VinFar/Tiki-Desklamp/Photos/IMG_20170602_134848.jpg

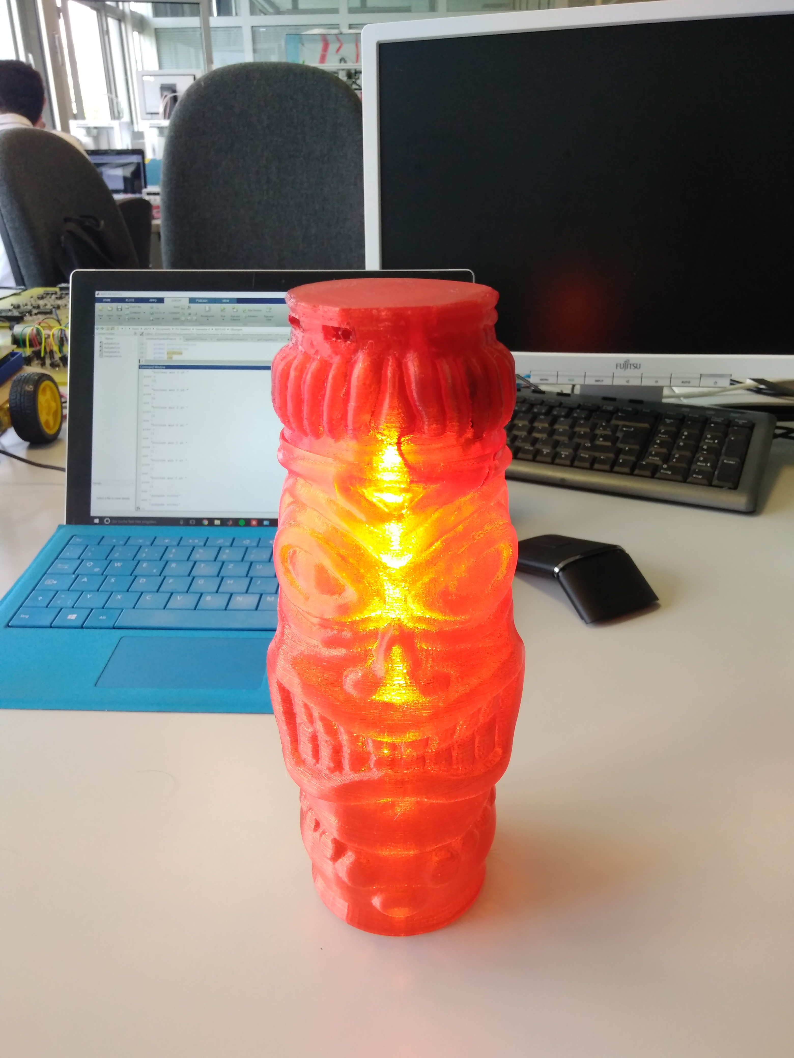
Photos/IMG_20170602_134848.jpg
