VinFar/Tiki-Desklamp/Photos/IMG_20170602_134851.jpg

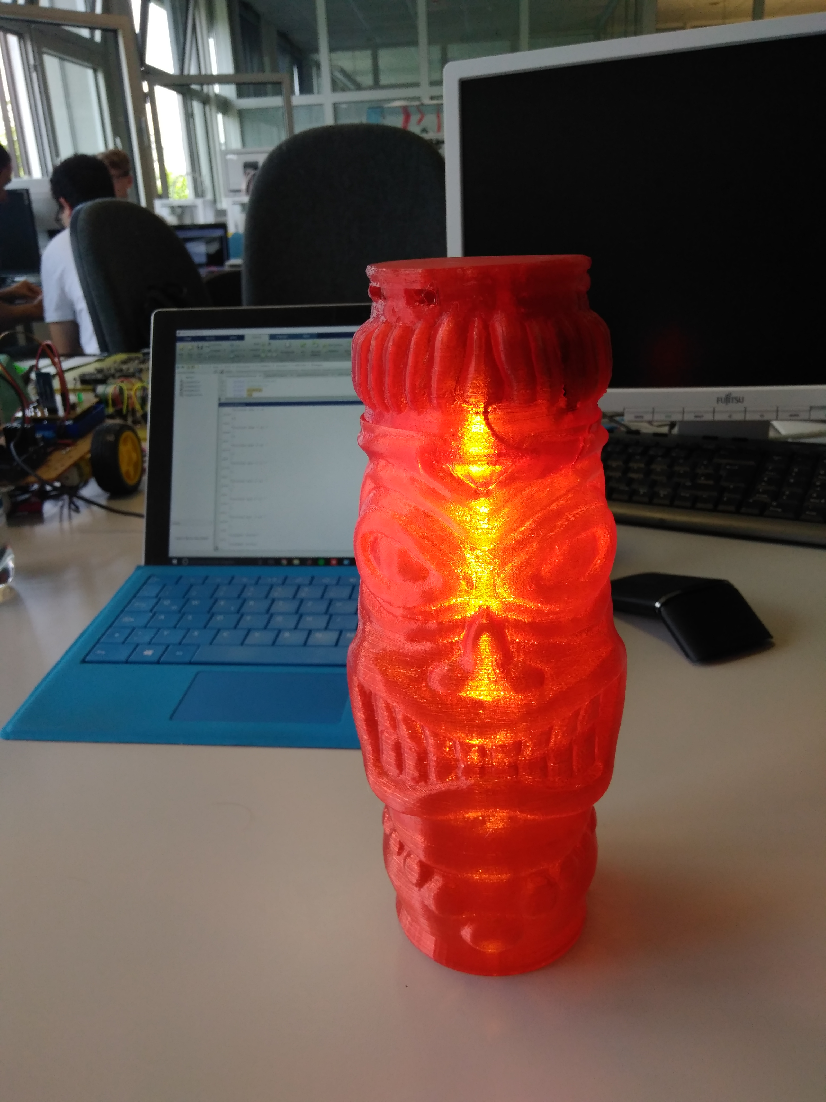
Photos/IMG_20170602_134851.jpg
