VinFar/Tiki-Desklamp/Photos/IMG_20170602_134853.jpg

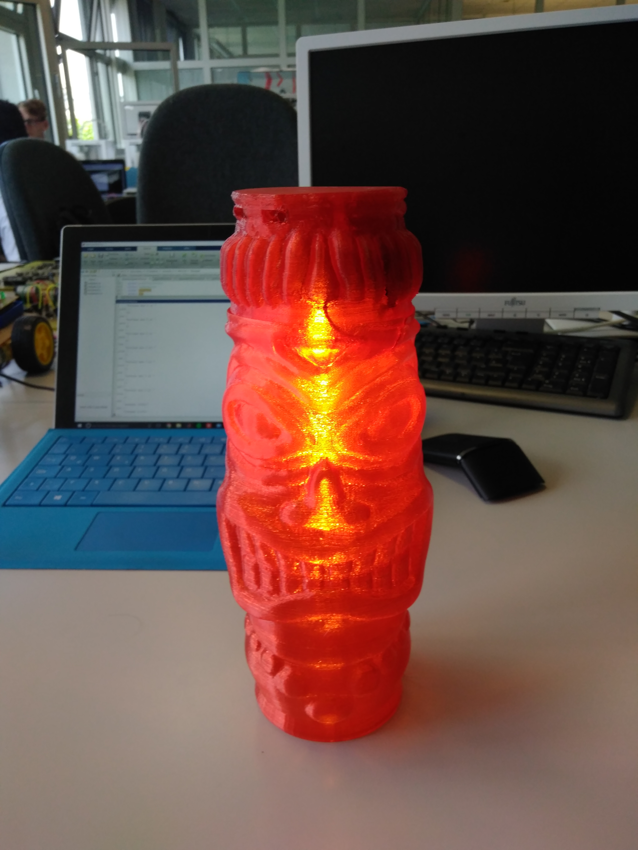
Photos/IMG_20170602_134853.jpg
