VinFar/Tiki-Desklamp/Photos/IMG_20170602_134902.jpg

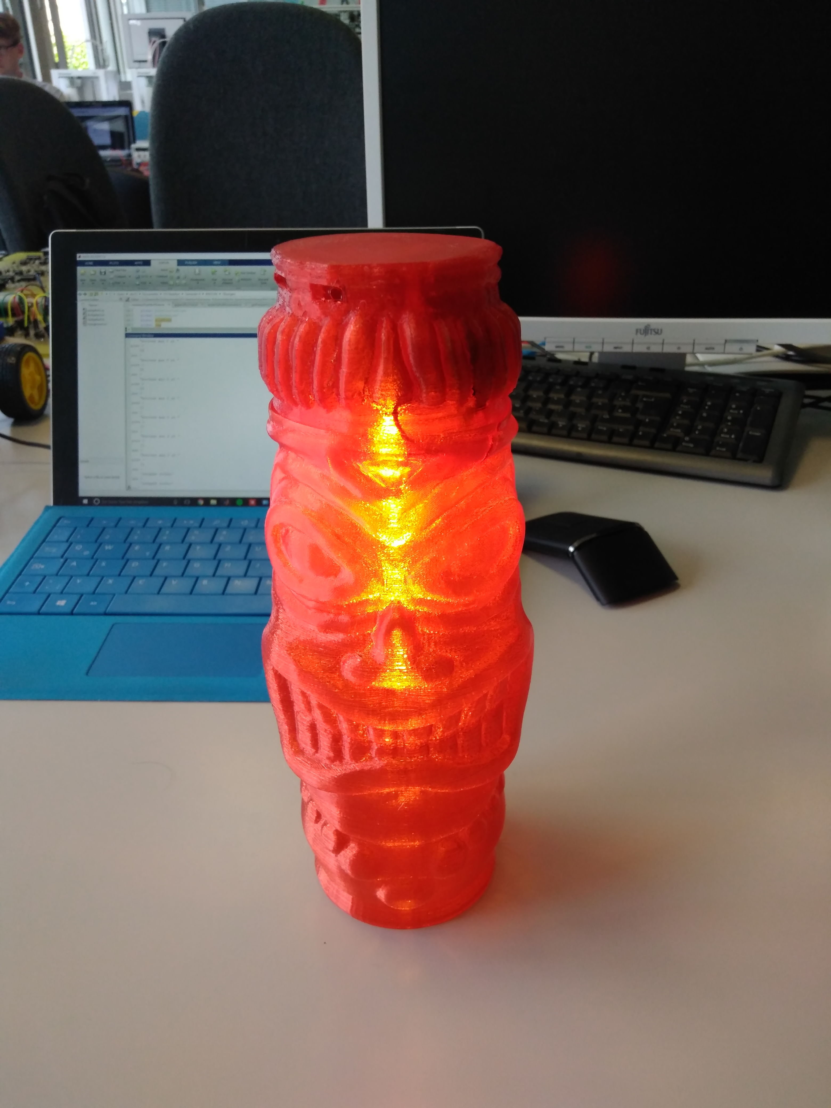
Photos/IMG_20170602_134902.jpg
