VinFar/Tiki-Desklamp/Photos/IMG_20170602_214356.jpg

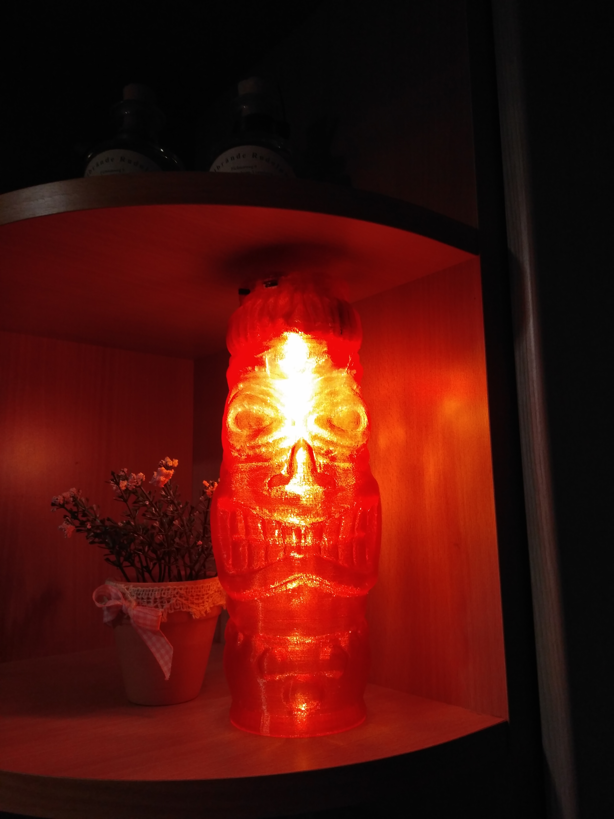
Photos/IMG_20170602_214356.jpg
