VinFar/Tiki-Desklamp/Photos/IMG_20170604_011007.jpg

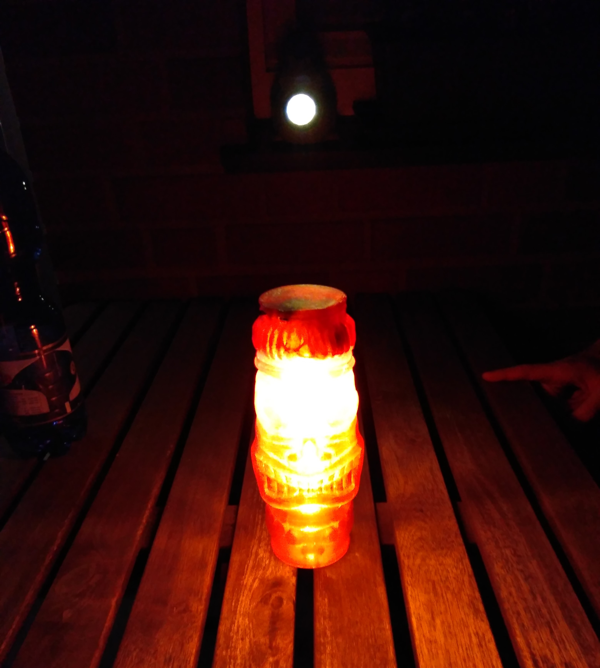
Photos/IMG_20170604_011007.jpg
