VinFar/Tiki-Desklamp/Photos/IMG_20170604_011009.jpg

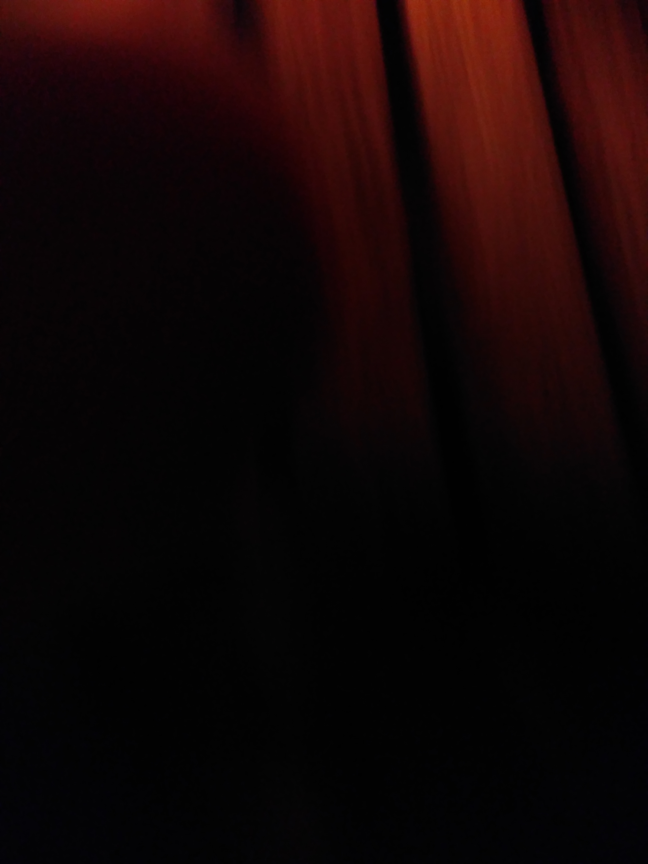
Photos/IMG_20170604_011009.jpg
