VinFar/Tiki-Desklamp/Photos/IMG_20170604_011032.jpg

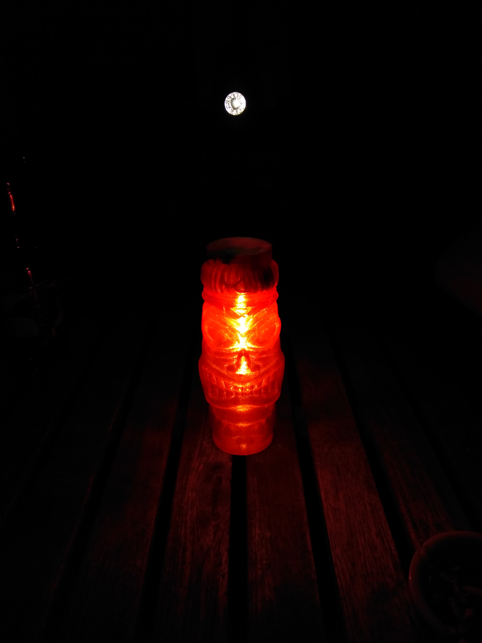
Photos/IMG_20170604_011032.jpg
