VinFar/Tiki-Desklamp/Photos/IMG_20170604_015317.jpg

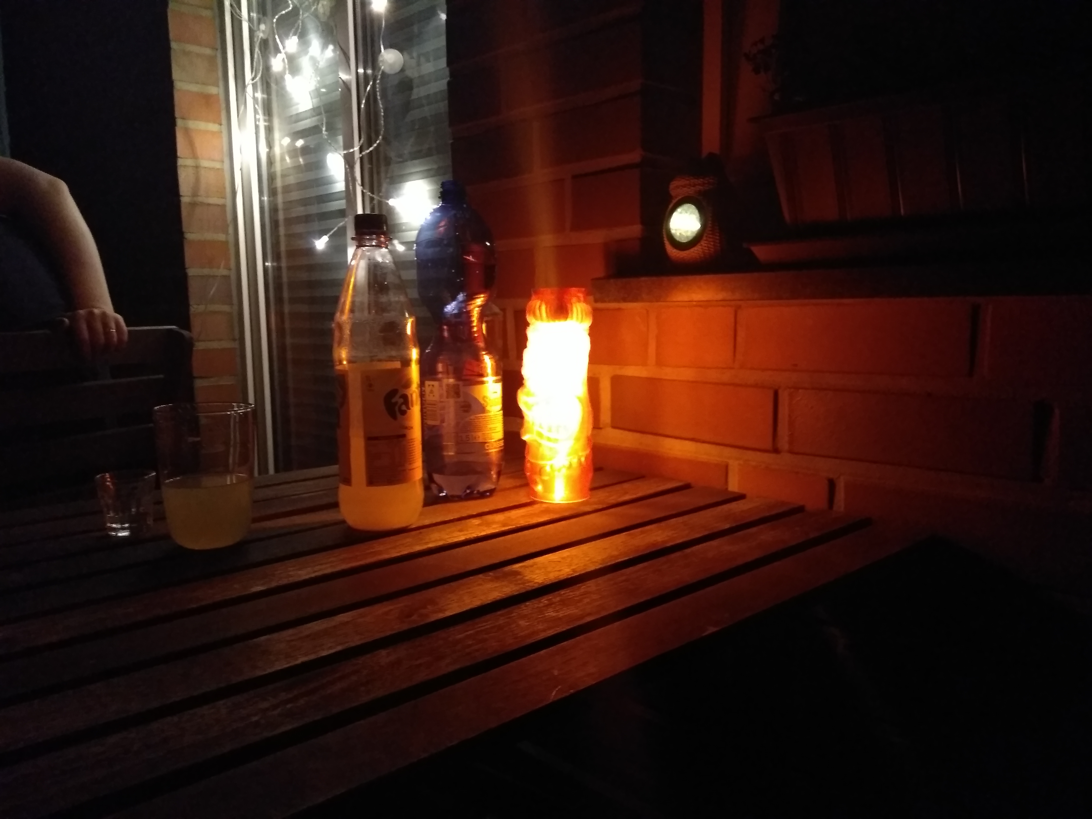
Photos/IMG_20170604_015317.jpg
