VinFar/Tiki-Desklamp/Photos/IMG_20170613_182519.jpg

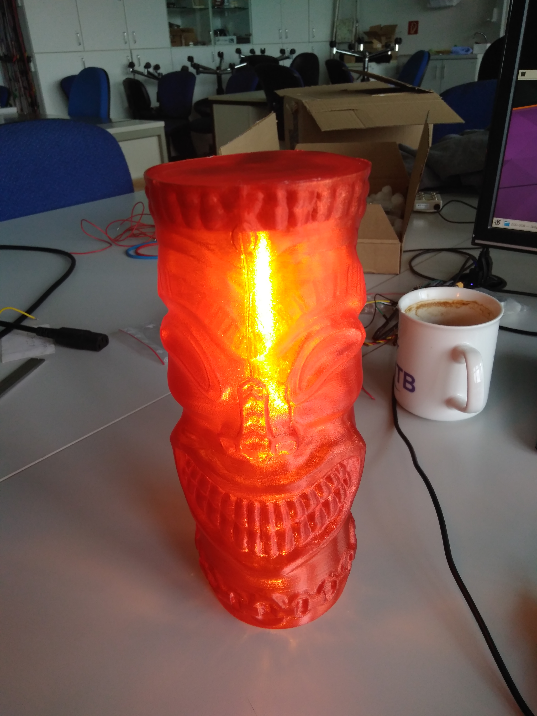
Photos/IMG_20170613_182519.jpg
