VinFar/Tiki-Desklamp/Photos/IMG_20170613_182521.jpg

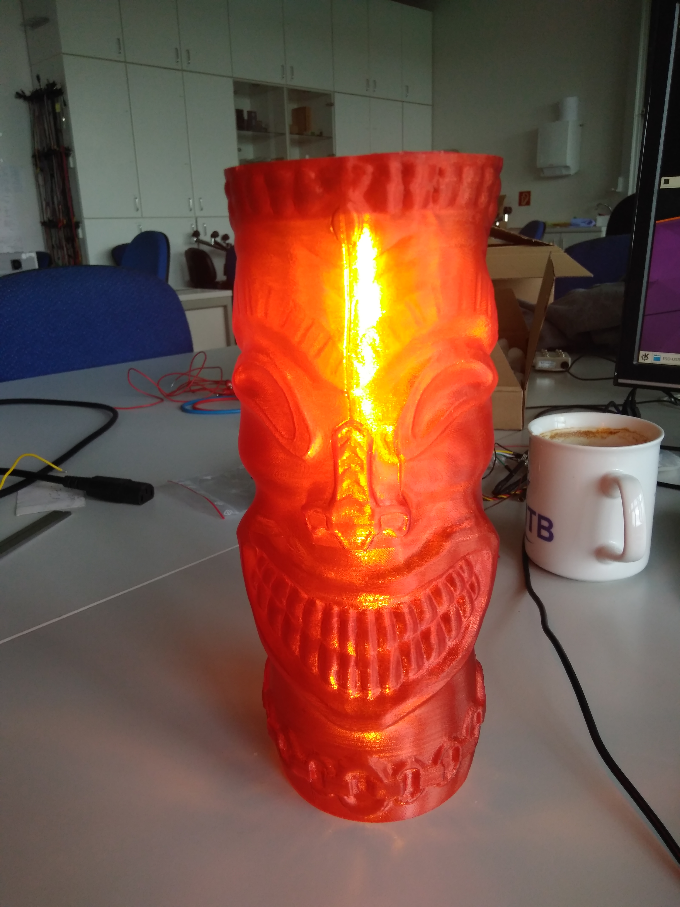
Photos/IMG_20170613_182521.jpg
