VinFar/Tiki-Desklamp/Photos/IMG_20170613_182523.jpg

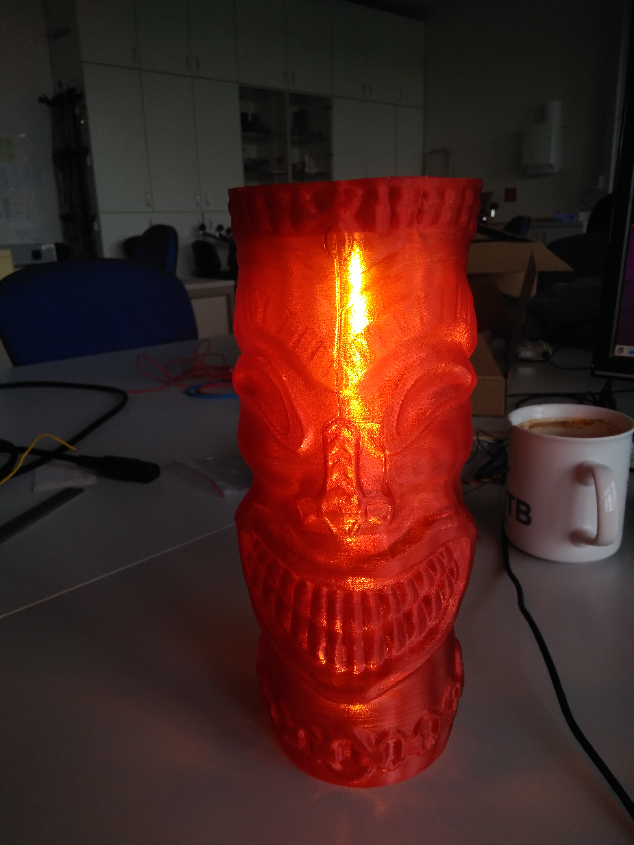
Photos/IMG_20170613_182523.jpg
