VinFar/Tiki-Desklamp/Photos/IMG_20170613_182524.jpg

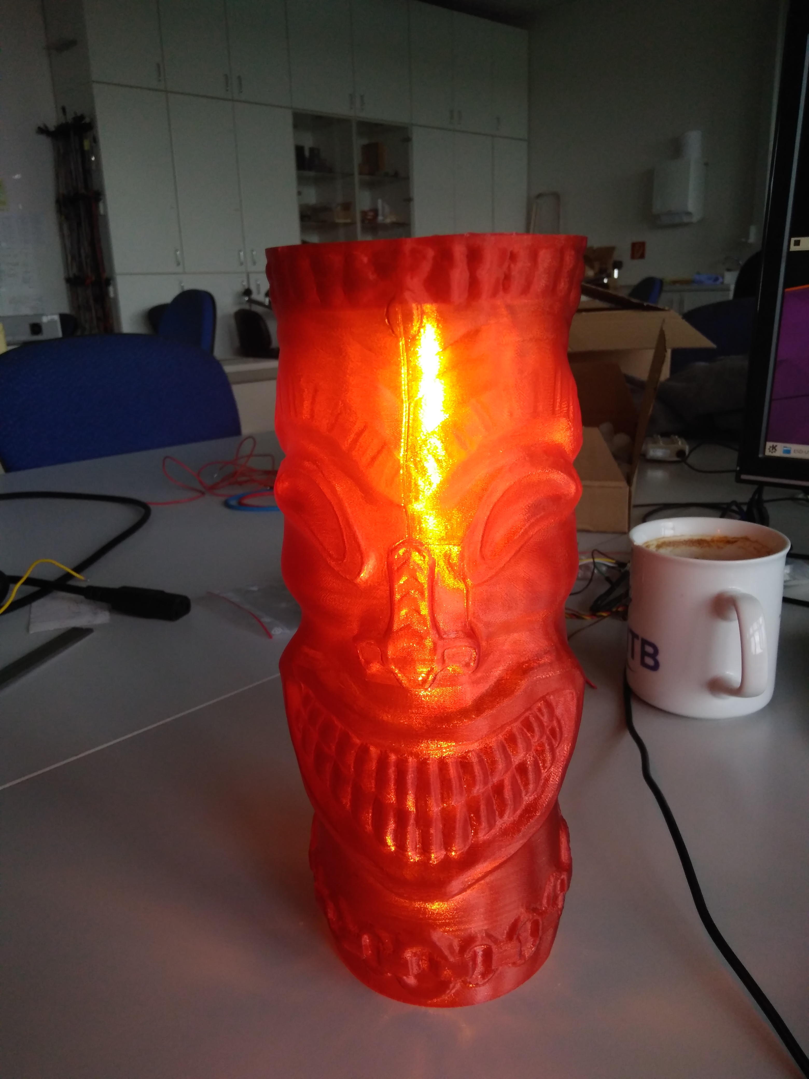
Photos/IMG_20170613_182524.jpg
