VinFar/Tiki-Desklamp/Photos/IMG_20170614_215922.jpg

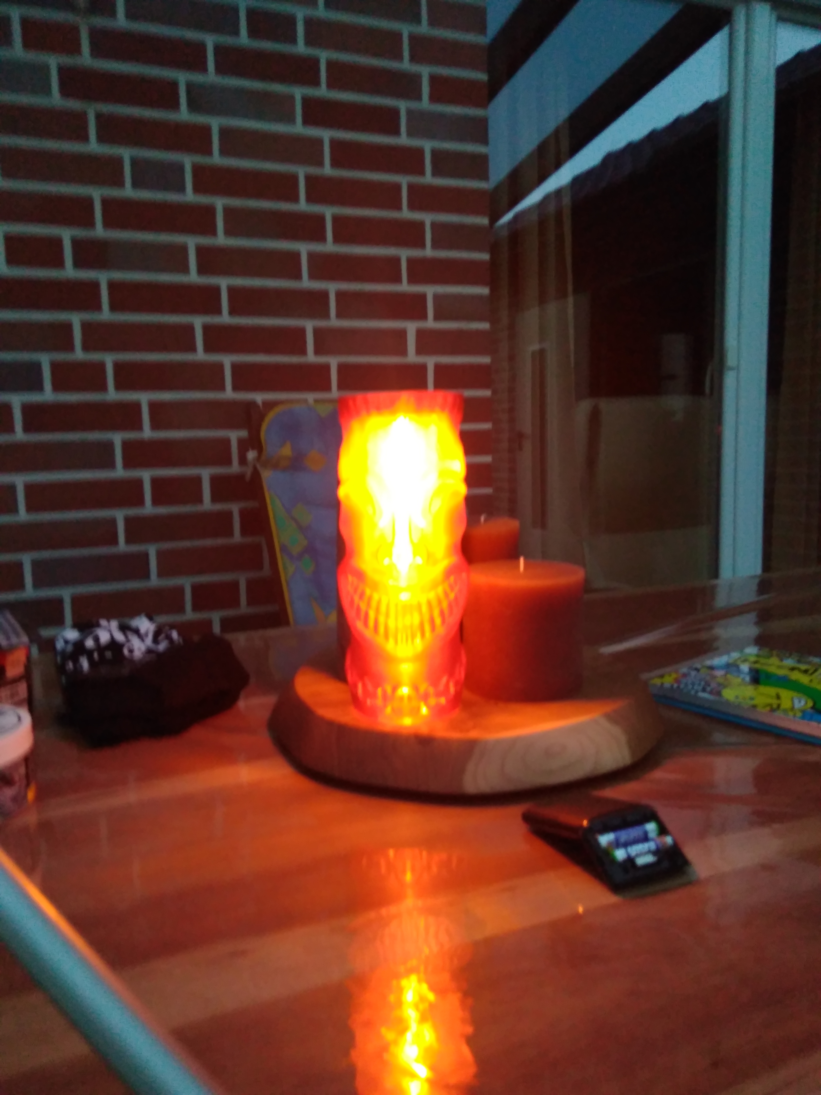
Photos/IMG_20170614_215922.jpg
