VinFar/Tiki-Desklamp/Photos/IMG_20170614_215926.jpg

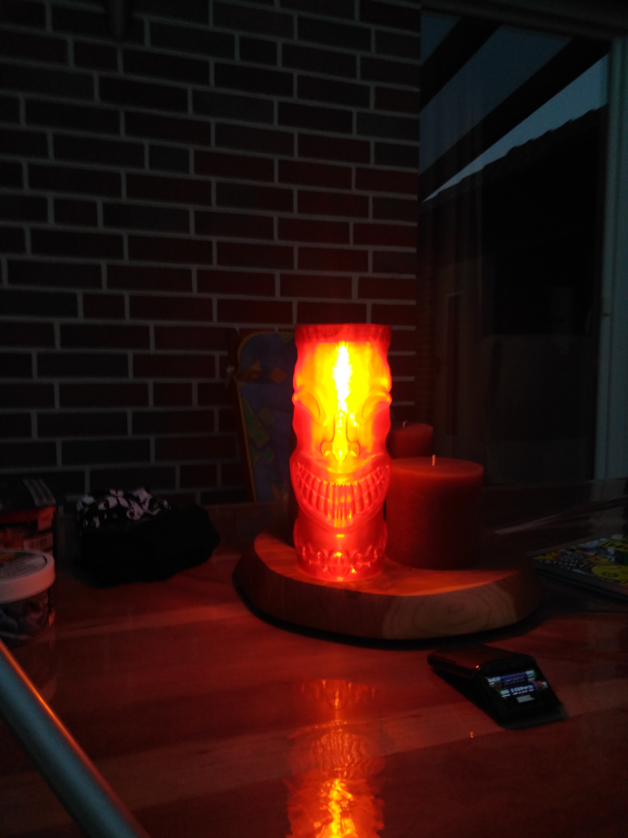
Photos/IMG_20170614_215926.jpg
