VinFar/Tiki-Desklamp/Photos/IMG_20170614_215931.jpg

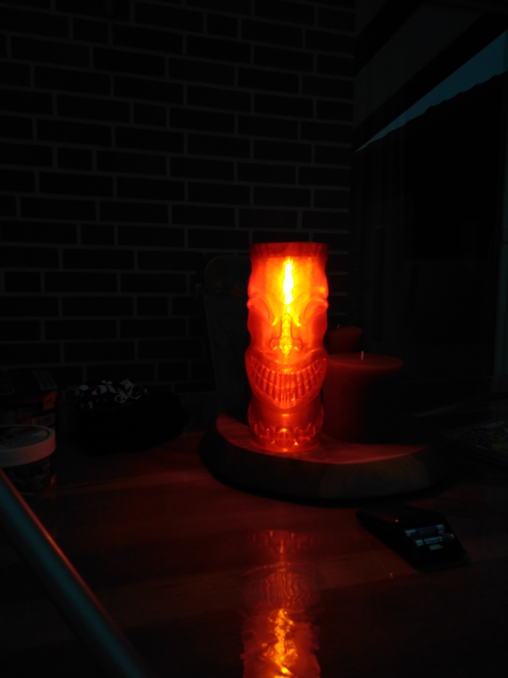
Photos/IMG_20170614_215931.jpg
