VinFar/Tiki-Desklamp/Photos/IMG_20170617_181317.jpg

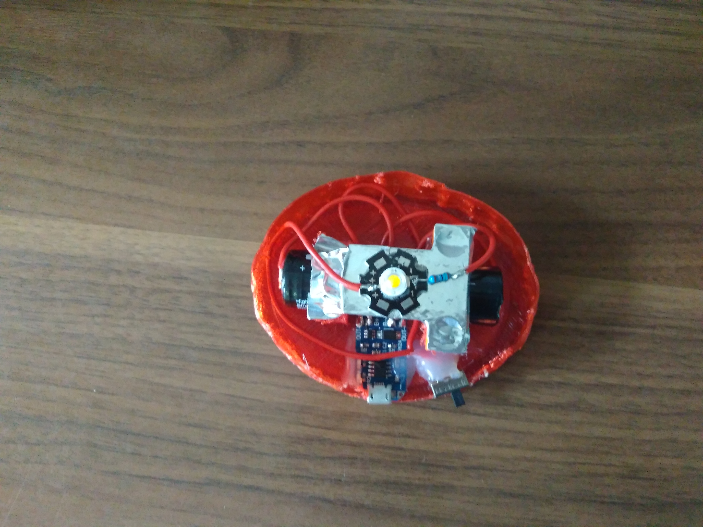
Photos/IMG_20170617_181317.jpg
