VinFar/Tiki-Desklamp/Photos/IMG_20170819_114427.jpg

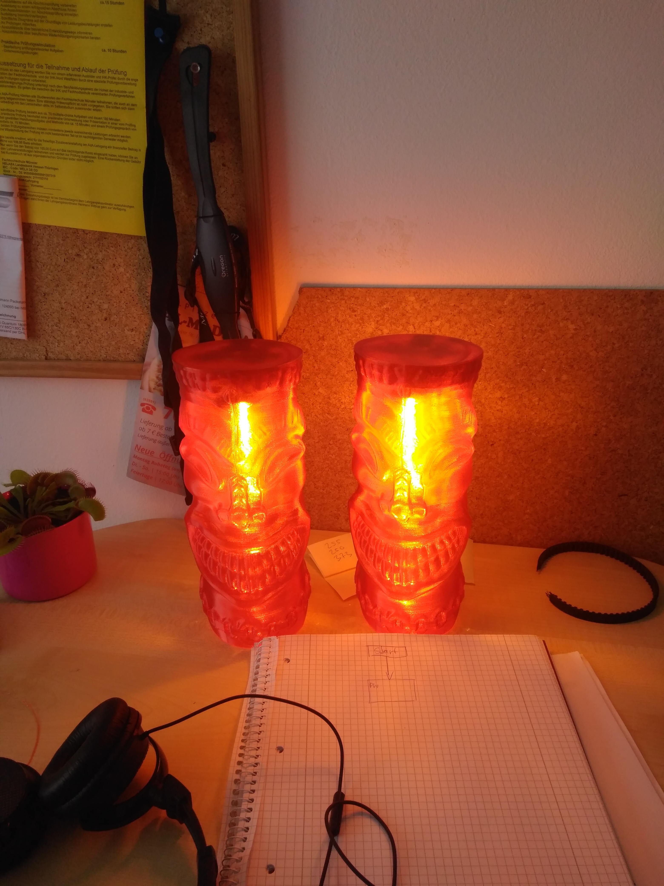
Photos/IMG_20170819_114427.jpg
